andrewmcknight/ski-trax/diagrams/ht_wifi_lora_32_v3_pinmap.png

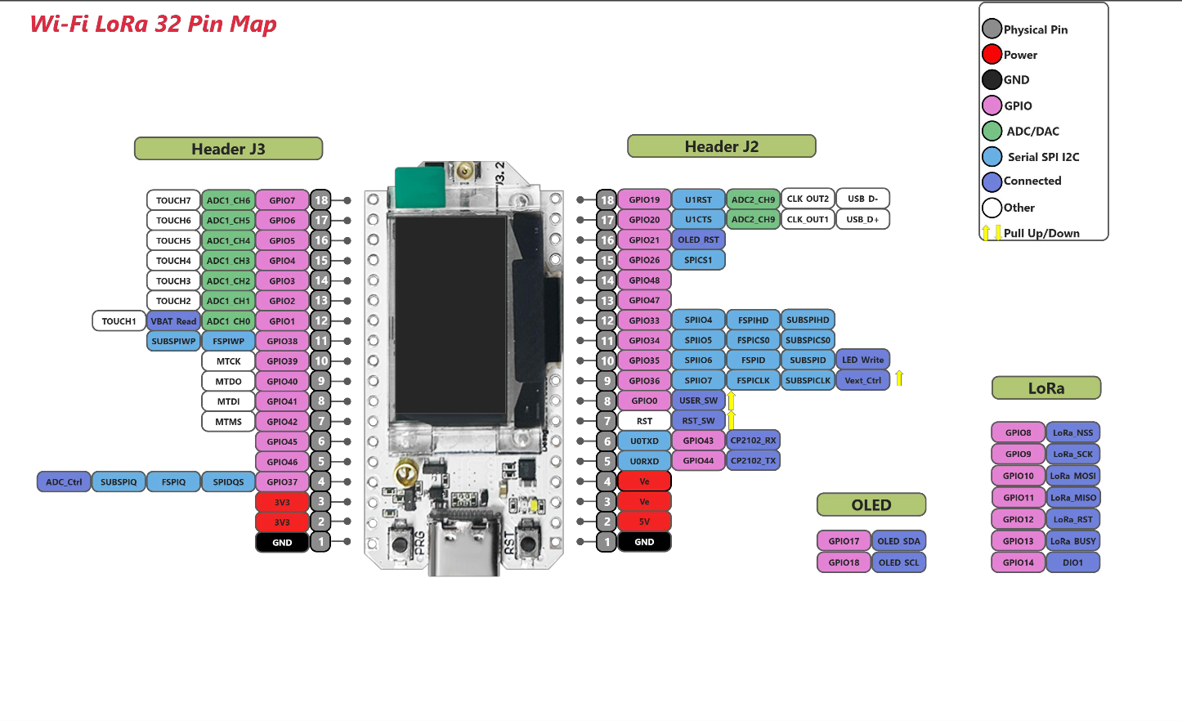
diagrams/ht_wifi_lora_32_v3_pinmap.png
