andrewmcknight/ski-trax/diagrams/pcb1.png

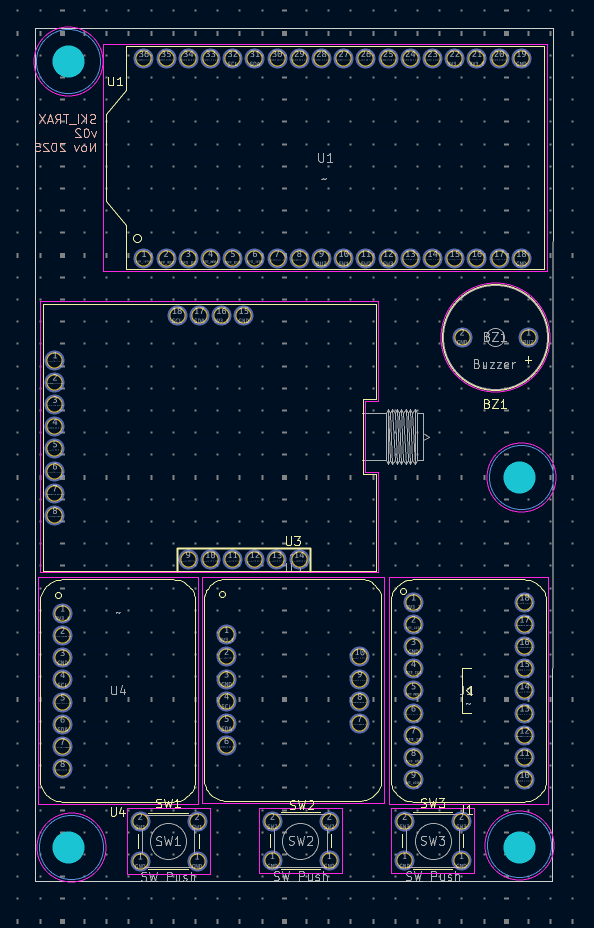
diagrams/pcb1.png
