andrewmcknight/ski-trax/diagrams/pcb2.png

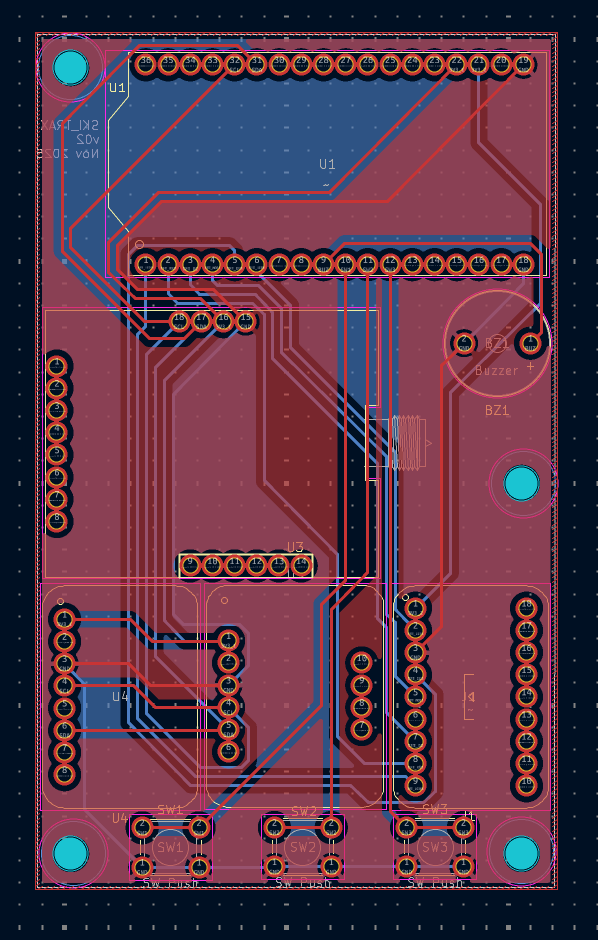
diagrams/pcb2.png
