andrewmcknight/ski-trax/images/Artboard 1.png

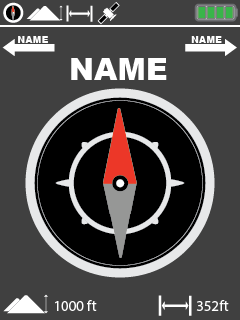
images/Artboard 1.png
