andrewmcknight/ski-trax/images/compass/full/compass_000.png

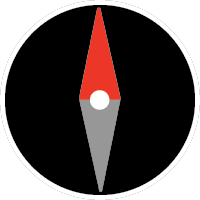
images/compass/full/compass_000.png
