andrewmcknight/ski-trax/images/compass/full/compass_010.png

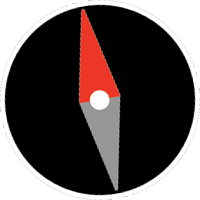
images/compass/full/compass_010.png
