andrewmcknight/ski-trax/images/compass/full/compass_050.png

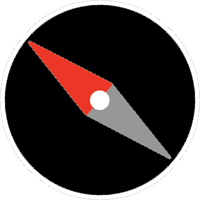
images/compass/full/compass_050.png
