andrewmcknight/ski-trax/images/compass/full/compass_070.png

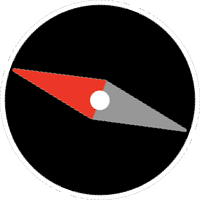
images/compass/full/compass_070.png
