andrewmcknight/ski-trax/images/compass/full/compass_110.png

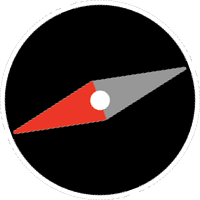
images/compass/full/compass_110.png
