andrewmcknight/ski-trax/images/compass/full/compass_120.png

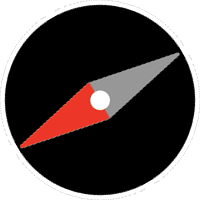
images/compass/full/compass_120.png
