andrewmcknight/ski-trax/images/compass/full/compass_140.png

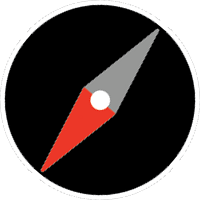
images/compass/full/compass_140.png
