andrewmcknight/ski-trax/images/compass/full/compass_160.png

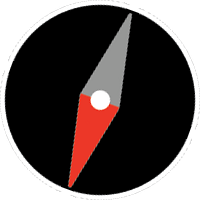
images/compass/full/compass_160.png
