andrewmcknight/ski-trax/images/compass/full/compass_170.png

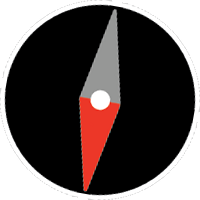
images/compass/full/compass_170.png
