andrewmcknight/ski-trax/images/compass/full/compass_180.png

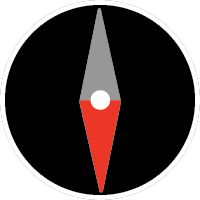
images/compass/full/compass_180.png
