andrewmcknight/ski-trax/images/compass/needles/needle_000.png

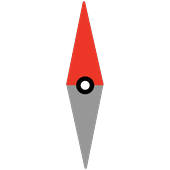
images/compass/needles/needle_000.png
