andrewmcknight/ski-trax/images/compass/needles/needle_010.png

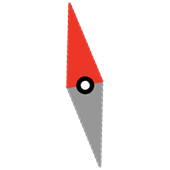
images/compass/needles/needle_010.png
