andrewmcknight/ski-trax/images/compass/needles/needle_020.png

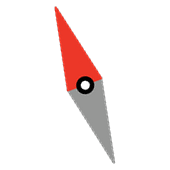
images/compass/needles/needle_020.png
