andrewmcknight/ski-trax/images/compass/needles/needle_030.png

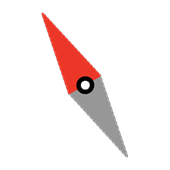
images/compass/needles/needle_030.png
