andrewmcknight/ski-trax/images/compass/needles/needle_040.png

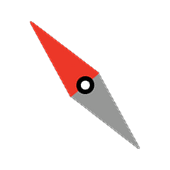
images/compass/needles/needle_040.png
