andrewmcknight/ski-trax/images/compass/needles/needle_050.png

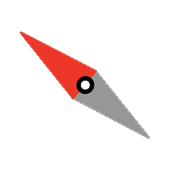
images/compass/needles/needle_050.png
