andrewmcknight/ski-trax/images/compass/needles/needle_060.png

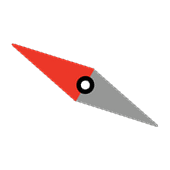
images/compass/needles/needle_060.png
