andrewmcknight/ski-trax/images/compass/needles/needle_080.png

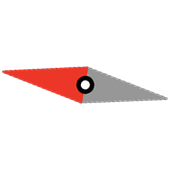
images/compass/needles/needle_080.png
