andrewmcknight/ski-trax/images/compass/needles/needle_110.png

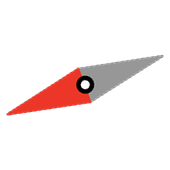
images/compass/needles/needle_110.png
