andrewmcknight/ski-trax/images/compass/needles/needle_120.png

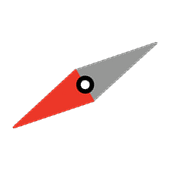
images/compass/needles/needle_120.png
