andrewmcknight/ski-trax/images/compass/needles/needle_130.png

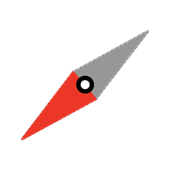
images/compass/needles/needle_130.png
