andrewmcknight/ski-trax/images/compass/needles/needle_140.png

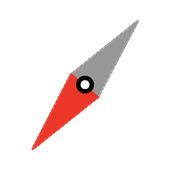
images/compass/needles/needle_140.png
