andrewmcknight/ski-trax/images/compass/needles/needle_150.png

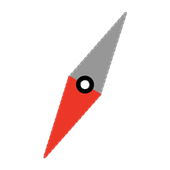
images/compass/needles/needle_150.png
