andrewmcknight/ski-trax/images/compass/needles/needle_160.png

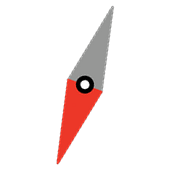
images/compass/needles/needle_160.png
