andrewmcknight/ski-trax/images/compass/needles/needle_170.png

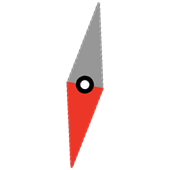
images/compass/needles/needle_170.png
