andrewmcknight/ski-trax/images/compass/wheel.png

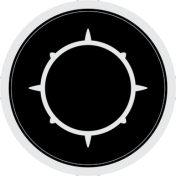
images/compass/wheel.png
