andrewmcknight/ski-trax/images/FullUI_240x320.png

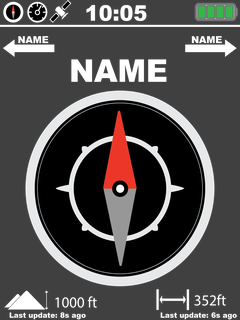
images/FullUI_240x320.png
