andrewmcknight/ski-trax/images/FullUI_BlackBG_240x320.png

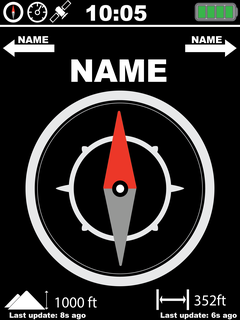
images/FullUI_BlackBG_240x320.png
