andrewmcknight/ski-trax/code/io_tests/sparkfun_max_m10s_test/sparkfun_max_m10s_test.ino

/*
 * (WORKING)
 * MAX-M10S GPS Test Program
 * Using SparkFun u-blox GNSS Arduino Library
 * 
 * Hardware Connections:
 * - SDA: GPIO 48
 * - SCL: GPIO 47
 * - I2C Address: 0x42 (fixed)
 * 
 * Installation:
 * 1. Open Arduino IDE
 * 2. Go to Tools > Manage Libraries
 * 3. Search for "SparkFun u-blox GNSS"
 * 4. Install "SparkFun u-blox GNSS Arduino Library" by SparkFun Electronics
 * 
 * This enhanced version provides:
 * - Full GNSS constellation support (GPS, GLONASS, Galileo, BeiDou)
 * - Accurate position, velocity, and time data
 * - Satellite tracking information
 * - DOP (Dilution of Precision) values
 * - Professional-grade parsing
 */

#include <Wire.h>
#include <SparkFun_u-blox_GNSS_Arduino_Library.h>

// I2C Configuration
#define SDA_PIN 48
#define SCL_PIN 47

#define VEXT_CTRL 36

// Create GNSS object
SFE_UBLOX_GNSS myGNSS;

// Status tracking
unsigned long lastDisplay = 0;
unsigned long startTime = 0;
bool gpsInitialized = false;

void setup() {
  Serial.begin(115200);
  delay(1000);

  // === ENABLE VEXT POWER RAIL ===
  pinMode(VEXT_CTRL, OUTPUT);
  digitalWrite(VEXT_CTRL, LOW);   // Turn on Vext 3.3V output
  delay(50); // give sensors time to power up
  
  Serial.println("\n\n=============================================");
  Serial.println("    MAX-M10S GPS Test - Enhanced Version");
  Serial.println("=============================================\n");
  
  // Initialize I2C
  Wire.begin(SDA_PIN, SCL_PIN);
  Wire.setClock(400000); // 400kHz for faster communication
  
  Serial.printf("I2C initialized on SDA=%d, SCL=%d\n", SDA_PIN, SCL_PIN);
  Serial.println("I2C Clock: 400kHz");
  
  // Initialize GNSS module
  Serial.println("\nConnecting to MAX-M10S...");
  
  if (myGNSS.begin(Wire) == false) {
    Serial.println("\n✗ GPS module NOT detected!");
    Serial.println("\nTroubleshooting:");
    Serial.println("  1. Check I2C connections:");
    Serial.println("     - SDA to GPIO 47");
    Serial.println("     - SCL to GPIO 48");
    Serial.println("  2. Verify 3.3V power and GND");
    Serial.println("  3. Ensure external antenna is connected");
    Serial.println("  4. Check I2C pullup resistors (Qwiic has them)");
    Serial.println("\nHalting...");
    while(1) delay(1000);
  }
  
  Serial.println("✓ GPS module detected!\n");
  
  // Configure GNSS
  configureGNSS();
  
  gpsInitialized = true;
  startTime = millis();
  
  Serial.println("\n============================================");
  Serial.println("Waiting for satellite fix...");
  Serial.println("Expected time: 24-60 seconds (cold start)");
  Serial.println("Make sure you're outdoors with clear sky view");
  Serial.println("============================================\n");
}

void loop() {
  if (!gpsInitialized) return;
  
  // Display GPS data every 1 second
  if (millis() - lastDisplay > 1000) {
    lastDisplay = millis();
    displayGNSSData();
  }
  
  delay(100);
}

void configureGNSS() {
  Serial.println("Configuring GNSS...");
  
  // Set I2C output for UBX protocol
  myGNSS.setI2COutput(COM_TYPE_UBX);
  
  // Disable auto PVT caching - we'll request fresh data manually
  myGNSS.setAutoPVT(false);
  
  // Enable all GNSS constellations (MAX-M10S supports all)
  myGNSS.enableGNSS(true, SFE_UBLOX_GNSS_ID_GPS);      // GPS
  myGNSS.enableGNSS(true, SFE_UBLOX_GNSS_ID_GALILEO);  // Galileo
  myGNSS.enableGNSS(true, SFE_UBLOX_GNSS_ID_BEIDOU);   // BeiDou
  myGNSS.enableGNSS(true, SFE_UBLOX_GNSS_ID_GLONASS);  // GLONASS
  
  // Set navigation rate to 1Hz (1 update per second)
  myGNSS.setNavigationFrequency(1);
  
  // Set dynamic platform model
  // DYN_MODEL_PORTABLE is best for handheld/general use
  // Other options: AUTOMOTIVE, PEDESTRIAN, AIRBORNE_1G, etc.
  myGNSS.setDynamicModel(DYN_MODEL_PORTABLE);
  
  // Save configuration (optional - persists across power cycles)
  // myGNSS.saveConfiguration();
  
  Serial.println("✓ GNSS configured:");
  Serial.println("  - All constellations enabled");
  Serial.println("  - Update rate: 1 Hz");
  Serial.println("  - Dynamic model: Portable");
  Serial.println("  - Manual data refresh enabled");
  Serial.println();
}

void displayGNSSData() {
  // Request fresh data from GPS module - THIS IS CRITICAL!
  // Without this, we just get stale cached data
  if (myGNSS.getPVT() == false) {
    Serial.println("Warning: Failed to get fresh PVT data");
    return;
  }
  
  // Query module for latest data
  long latitude = myGNSS.getLatitude();      // Degrees * 10^-7
  long longitude = myGNSS.getLongitude();    // Degrees * 10^-7
  long altitude = myGNSS.getAltitude();      // mm above MSL
  long altitudeMSL = myGNSS.getAltitudeMSL(); // mm above mean sea level
  
  byte fixType = myGNSS.getFixType();
  byte satellites = myGNSS.getSIV();         // Satellites in View
  
  long speed = myGNSS.getGroundSpeed();      // mm/s
  long heading = myGNSS.getHeading();        // Degrees * 10^-5
  
  uint16_t pDOP = myGNSS.getPDOP();          // Position DOP * 100
  
  // Time information
  byte hour = myGNSS.getHour();
  byte minute = myGNSS.getMinute();
  byte second = myGNSS.getSecond();
  int year = myGNSS.getYear();
  byte month = myGNSS.getMonth();
  byte day = myGNSS.getDay();
  
  // Display header
  Serial.println("\n╔════════════════════════════════════════════════════════╗");
  Serial.println("║              MAX-M10S GNSS STATUS                      ║");
  Serial.println("╠════════════════════════════════════════════════════════╣");
  
  // Runtime
  unsigned long runtime = (millis() - startTime) / 1000;
  Serial.printf("║ Runtime: %02luh %02lum %02lus", runtime/3600, (runtime%3600)/60, runtime%60);
  Serial.print("                                    ║\n");
  Serial.println("╠════════════════════════════════════════════════════════╣");
  
  // Fix status
  Serial.print("║ Fix Type: ");
  switch(fixType) {
    case 0: Serial.print("No Fix      "); break;
    case 1: Serial.print("Dead Reckon "); break;
    case 2: Serial.print("2D Fix      "); break;
    case 3: Serial.print("3D Fix      "); break;
    case 4: Serial.print("GNSS+DR     "); break;
    case 5: Serial.print("Time Only   "); break;
    default: Serial.printf("Unknown (%d) ", fixType); break;
  }
  
  Serial.printf("   Satellites: %2d              ║\n", satellites);
  
  // Position DOP
  Serial.printf("║ PDOP: %4.2f", pDOP / 100.0);
  Serial.print("                                            ║\n");
  
  Serial.println("╠════════════════════════════════════════════════════════╣");
  
  if (fixType >= 2) {
    // Position
    Serial.printf("║ Latitude:   %3.7f°", latitude / 10000000.0);
    Serial.print("                          ║\n");
    Serial.printf("║ Longitude: %4.7f°", longitude / 10000000.0);
    Serial.print("                          ║\n");
    Serial.printf("║ Altitude:   %7.2f m (MSL: %7.2f m)", 
                  altitude / 1000.0, altitudeMSL / 1000.0);
    Serial.print("         ║\n");
    
    Serial.println("╠════════════════════════════════════════════════════════╣");
    
    // Motion
    Serial.printf("║ Speed:      %6.2f km/h", (speed / 1000.0) * 3.6);
    Serial.print("                             ║\n");
    Serial.printf("║ Heading:    %6.2f°", heading / 100000.0);
    Serial.print("                                  ║\n");
    
    Serial.println("╠════════════════════════════════════════════════════════╣");
    
    // Time (UTC)
    Serial.printf("║ UTC Time:   %04d-%02d-%02d %02d:%02d:%02d", 
                  year, month, day, hour, minute, second);
    Serial.print("                 ║\n");
    
    // Calculate accuracy estimates
    long hAcc = myGNSS.getHorizontalAccuracy(); // mm
    long vAcc = myGNSS.getVerticalAccuracy();   // mm
    
    Serial.println("╠════════════════════════════════════════════════════════╣");
    Serial.printf("║ Horiz Accuracy: ±%.2f m   Vert Accuracy: ±%.2f m", 
                  hAcc / 1000.0, vAcc / 1000.0);
    Serial.print("  ║\n");
    
  } else {
    Serial.println("║                                                        ║");
    Serial.println("║              🛰️  ACQUIRING SATELLITES...               ║");
    Serial.println("║                                                        ║");
    Serial.printf("║         Satellites visible: %2d                        ║\n", satellites);
    
    if (satellites == 0) {
      Serial.println("║                                                        ║");
      Serial.println("║  ⚠️  Check:                                            ║");
      Serial.println("║     • Antenna connected to SMA connector               ║");
      Serial.println("║     • Clear view of sky (outdoors preferred)           ║");
      Serial.println("║     • No obstructions (buildings, trees)               ║");
    }
  }
  
  Serial.println("╚════════════════════════════════════════════════════════╝\n");
  
  // Display constellation info
  displayConstellationInfo();
}

void displayConstellationInfo() {
  // Get info about satellites from each constellation
  Serial.println("Constellation Status:");
  Serial.println("┌──────────┬───────────┬────────────────┐");
  Serial.println("│ System   │ Enabled   │ Satellites     │");
  Serial.println("├──────────┼───────────┼────────────────┤");
  
  // Note: Getting detailed constellation info requires more advanced UBX parsing
  // For now, show that all constellations are enabled
  Serial.println("│ GPS      │    ✓      │ Tracking       │");
  Serial.println("│ GLONASS  │    ✓      │ Tracking       │");
  Serial.println("│ Galileo  │    ✓      │ Tracking       │");
  Serial.println("│ BeiDou   │    ✓      │ Tracking       │");
  Serial.println("└──────────┴───────────┴────────────────┘");
  Serial.println();
}
